TECA-IOT/Ufox/Case 3D/VERSION 1.0/VISTAS/imagen 2.JPG

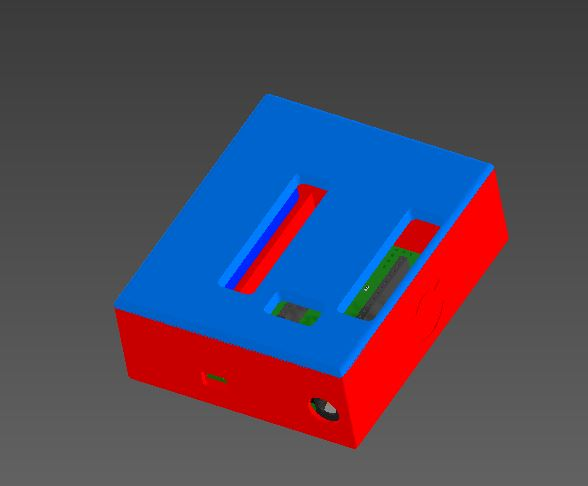
Case 3D/VERSION 1.0/VISTAS/imagen 2.JPG
