TECA-IOT/Ufox/Case 3D/VERSION 1.0/VISTAS/imagen.JPG

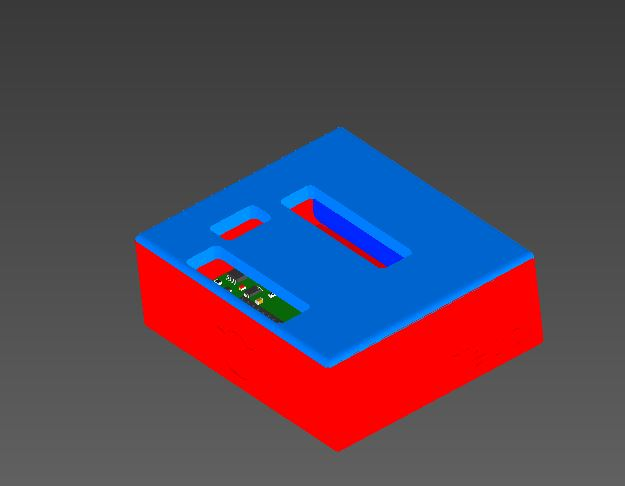
Case 3D/VERSION 1.0/VISTAS/imagen.JPG
