TECA-IOT/Ufox/image/Ufox.jpg

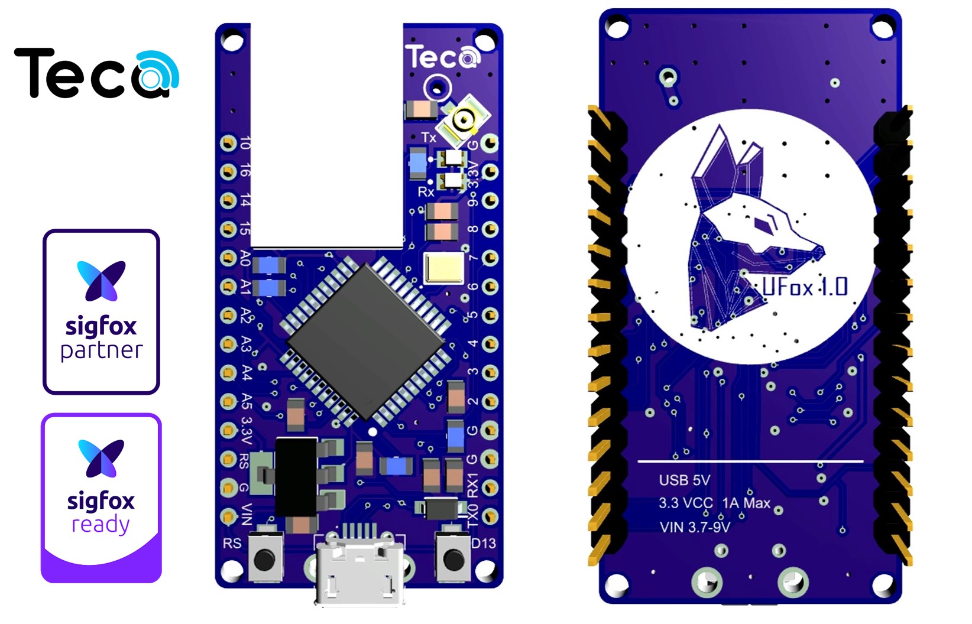
image/Ufox.jpg
