TECA-IOT/Ufox/image/ufox_v1_2.png

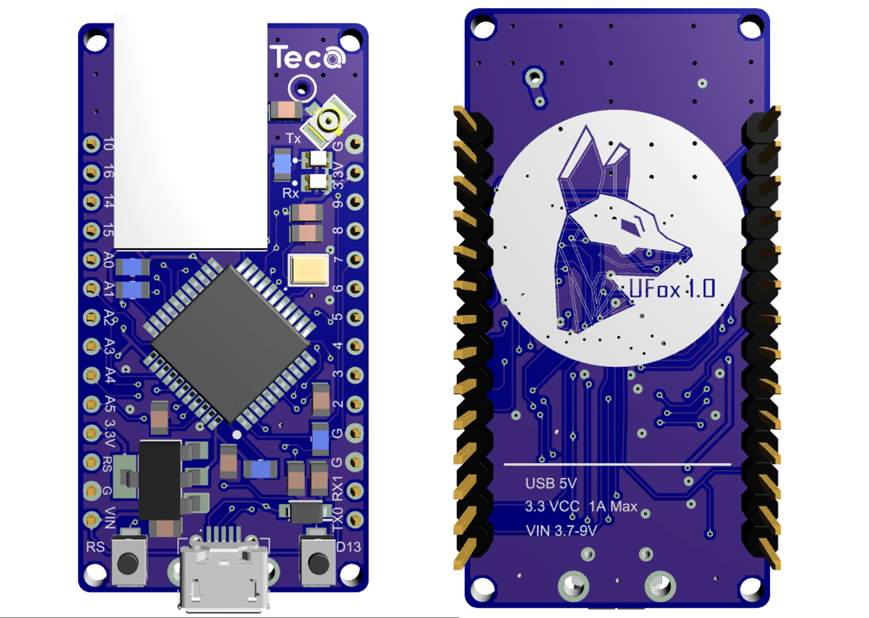
image/ufox_v1_2.png
