TECA-IOT/Ufox/UFOX BOARD  FRITZING/ufox_fritzing.png

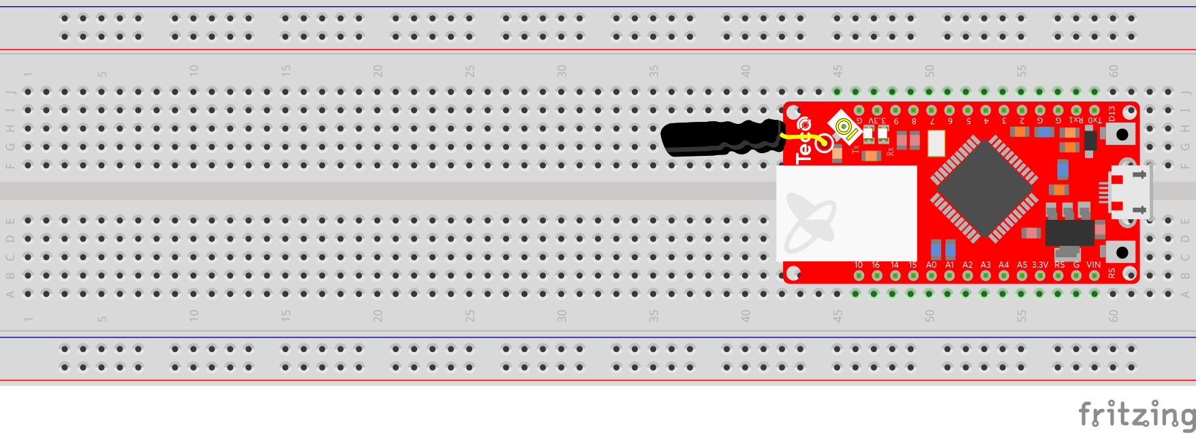
UFOX BOARD FRITZING/ufox_fritzing.png
